Supercookiegaming/PCIe-Aux-Signal-Breakout/Images/3D/Full-Profile-Adapater-Bracket-Side.PNG

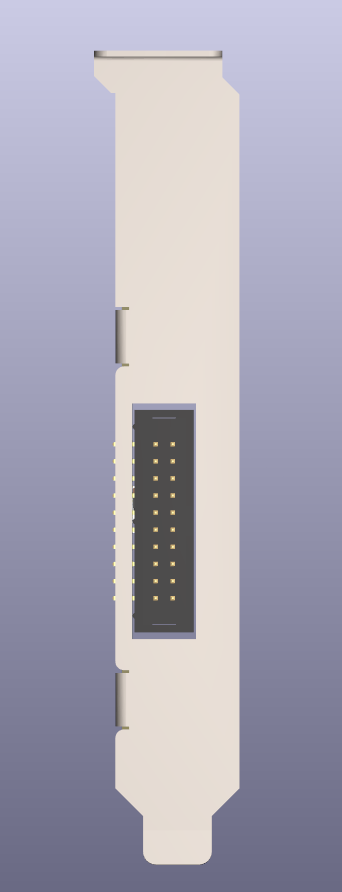
Images/3D/Full-Profile-Adapater-Bracket-Side.PNG
