Supercookiegaming/PCIe-Aux-Signal-Breakout/Images/3D/Low-Profile-Adapater-Bracket-Side.PNG

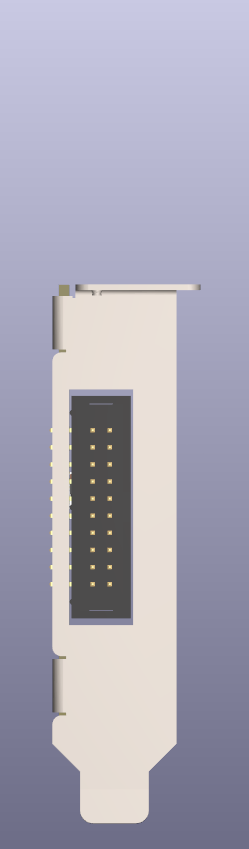
Images/3D/Low-Profile-Adapater-Bracket-Side.PNG
